stepleton/voltmitten/powerup/mos_dram-1979_Mostek_Memory_Data_Book_and_Designers_Guide_Mar79-p108.png

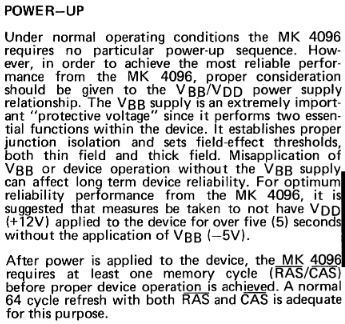
powerup/mos_dram-1979_Mostek_Memory_Data_Book_and_Designers_Guide_Mar79-p108.png
