stepleton/voltmitten/hardware/voltmitten.sch

## KiCad design hardware/voltmitten.sch (2021-11-13)

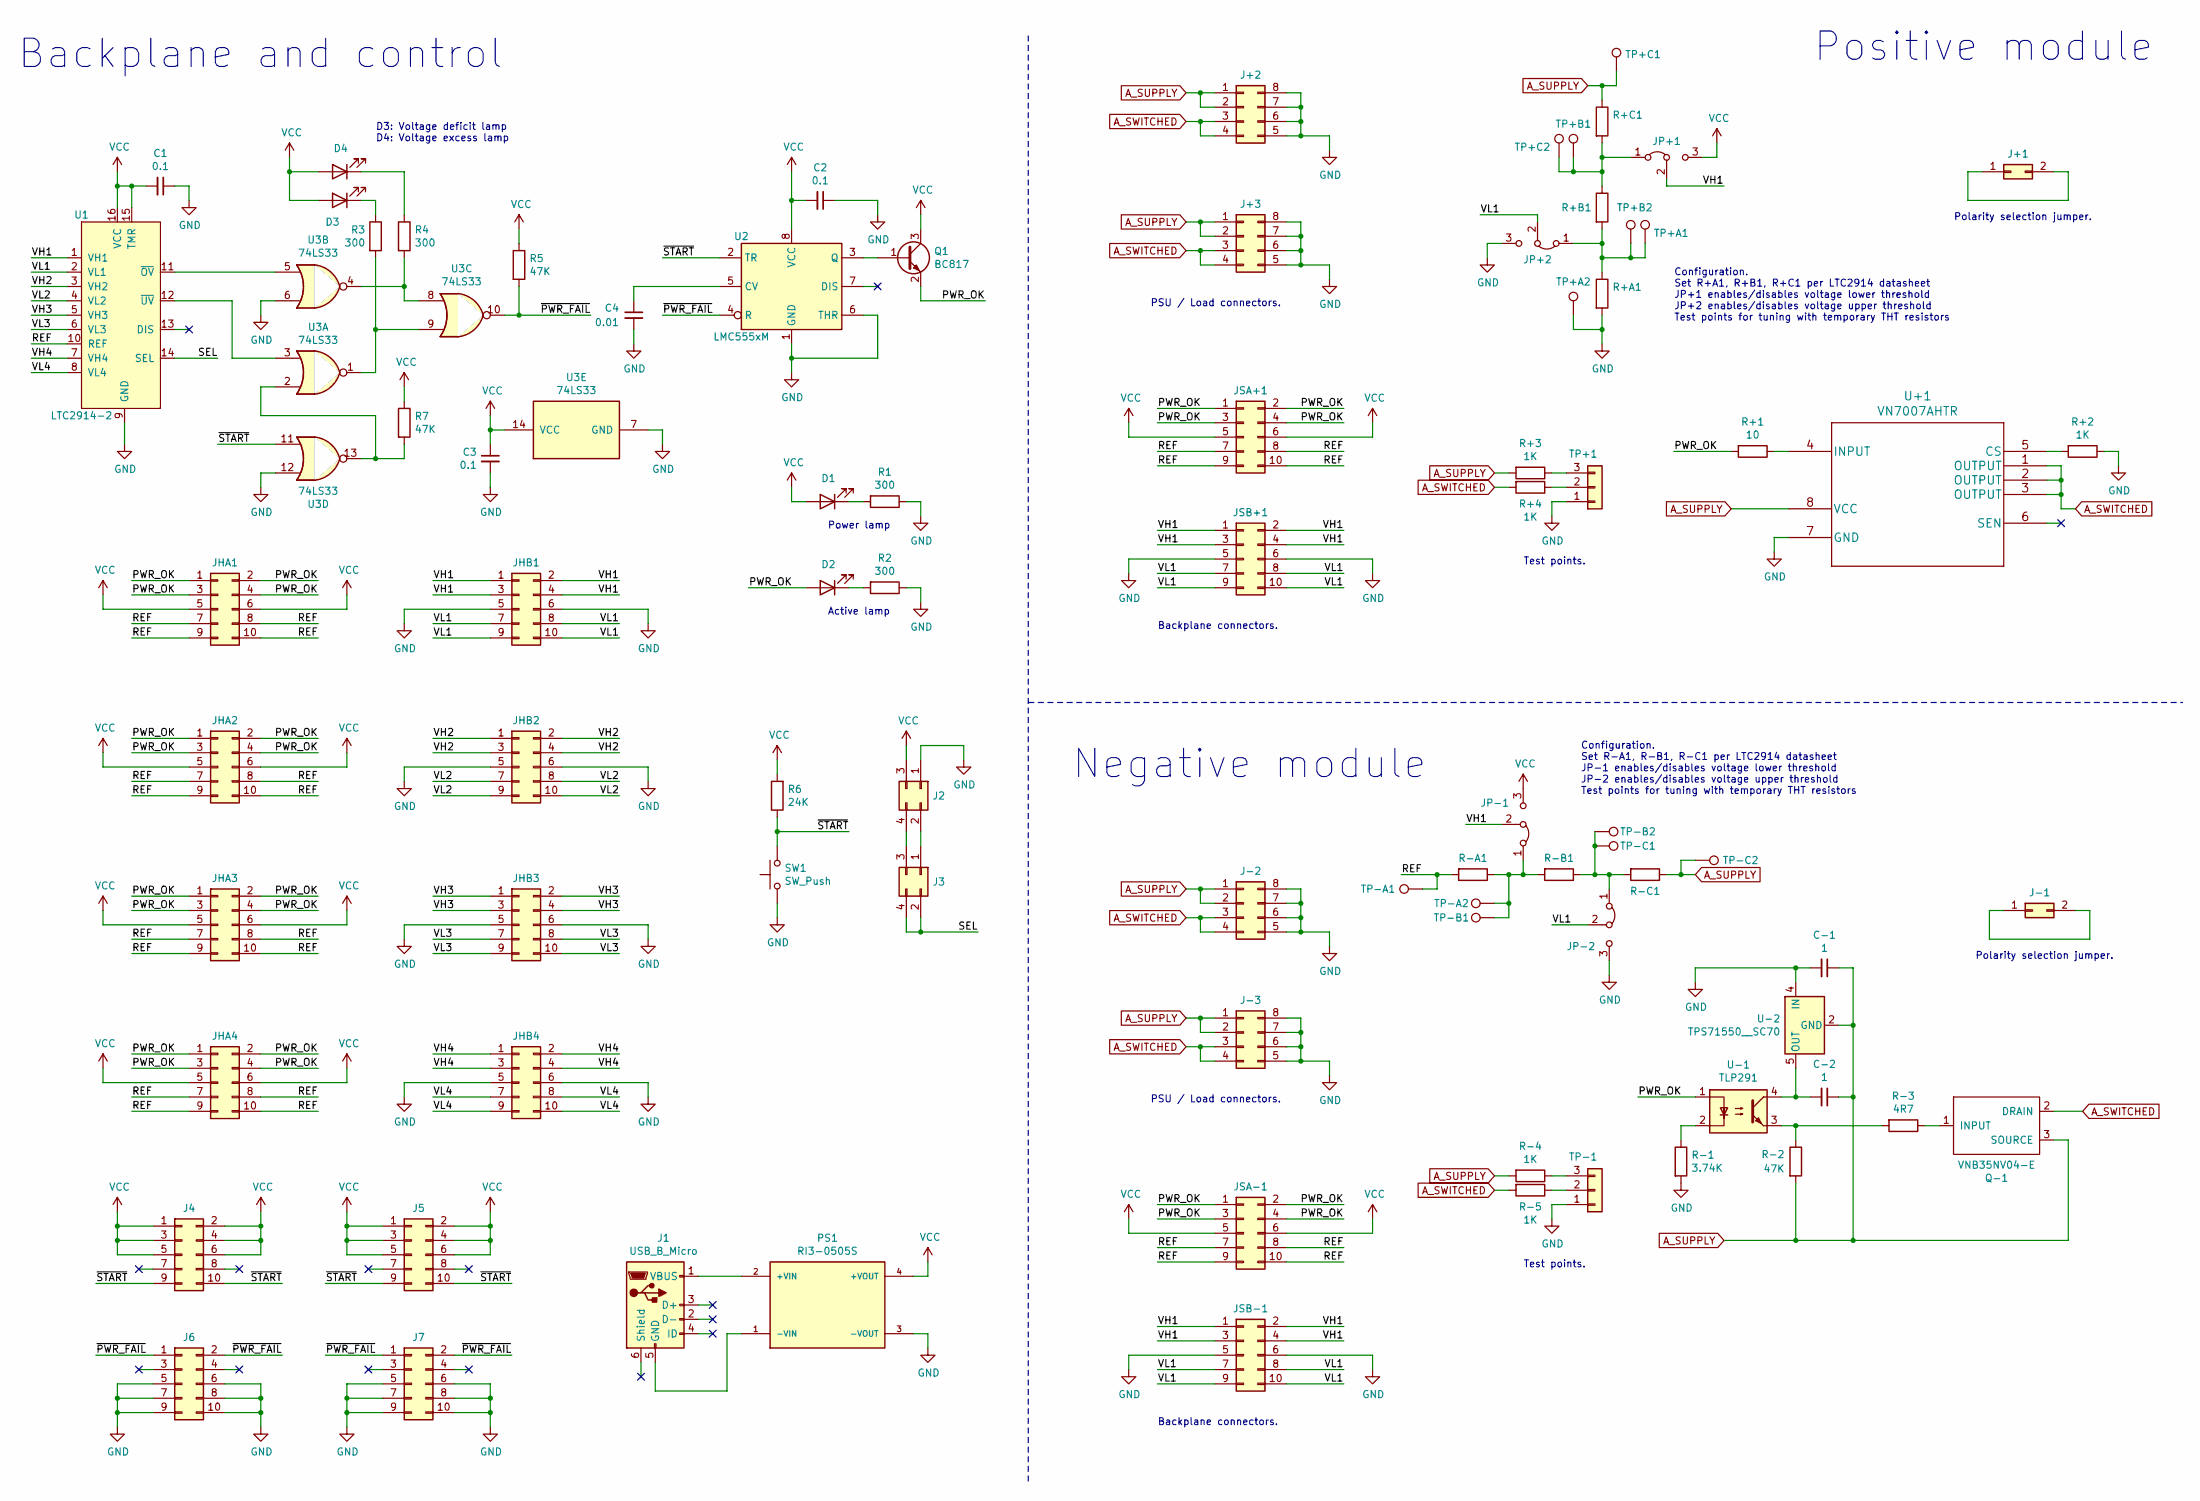
[picture p31: schematic voltmitten.sch]

Parts:
C1, C2, C3: 0.1; C_0603_1608Metric_Pad1.08x0.95mm_HandSolder
C4: 0.01; C_0603_1608Metric_Pad1.08x0.95mm_HandSolder
C-1, C-2: 1; C_0603_1608Metric_Pad1.08x0.95mm_HandSolder
D1, D2, D3, D4: SML-D12U1WT86‎; LED_0603_1608Metric_Pad1.05x0.95mm_HandSolder
J1: USB_B_Micro; USB_Micro-B_Amphenol_10103594-0001LF_Horizontal
J2, J3: Conn_02x02_Row_Letter_Last; PinSocket_2x02_P2.54mm_Vertical
J4, J6: Conn_02x05_Row_Letter_Last; PinHeader_2x05_P2.54mm_Horizontal
J5, J7: Conn_02x05_Row_Letter_Last; PinSocket_2x05_P2.54mm_Horizontal
J+1: Conn_02x01; PinHeader_1x02_P2.54mm_Vertical
J+2, J+3: Conn_02x04_Counter_Clockwise; TE_MATE-N-LOK_1-794073-x_2x04_P4.14mm_Vertical_no_boardlock
J-1: Conn_02x01; PinHeader_1x02_P2.54mm_Vertical
J-2, J-3: Conn_02x04_Counter_Clockwise; TE_MATE-N-LOK_1-794073-x_2x04_P4.14mm_Vertical_no_boardlock
JHA1, JHA2, JHA3, JHA4: Conn_02x05_Row_Letter_Last; PinHeader_2x05_P2.54mm_Vertical
JHB1, JHB2, JHB3, JHB4: Conn_02x05_Row_Letter_Last; PinHeader_2x05_P2.54mm_Vertical
JP+1, JP+2: Jumper_3_Bridged12; PinHeader_1x03_P2.00mm_Horizontal
JP-1, JP-2: Jumper_3_Bridged12; PinHeader_1x03_P2.00mm_Horizontal
JSA+1: Conn_02x05_Odd_Even; PinSocket_2x05_P2.54mm_Vertical
JSA-1: Conn_02x05_Odd_Even; PinSocket_2x05_P2.54mm_Vertical
JSB+1: Conn_02x05_Odd_Even; PinSocket_2x05_P2.54mm_Vertical
JSB-1: Conn_02x05_Odd_Even; PinSocket_2x05_P2.54mm_Vertical
PS1: RI3-0505S; CONV_RI3-0505S; PARTREV 3
Q1: BC817; SOT-23
Q-1: VNB35NV04-E; D2PAK
R1, R2, R3, R4: 300; R_0603_1608Metric_Pad0.98x0.95mm_HandSolder
R5, R7: 47K; R_0603_1608Metric_Pad0.98x0.95mm_HandSolder
R6: 24K; R_0603_1608Metric_Pad0.98x0.95mm_HandSolder
R+1: 10; R_0603_1608Metric_Pad0.98x0.95mm_HandSolder
R+2, R+3, R+4: 1K; R_0603_1608Metric_Pad0.98x0.95mm_HandSolder
R+A1: R; R_0603_1608Metric_Pad0.98x0.95mm_HandSolder
R+B1: R; R_0603_1608Metric_Pad0.98x0.95mm_HandSolder
R+C1: R; R_0603_1608Metric_Pad0.98x0.95mm_HandSolder
R-1: 3.74K; R_0603_1608Metric_Pad0.98x0.95mm_HandSolder
R-2: 47K; R_0603_1608Metric_Pad0.98x0.95mm_HandSolder
R-3: 4R7; R_0603_1608Metric_Pad0.98x0.95mm_HandSolder
R-4, R-5: 1K; R_0603_1608Metric_Pad0.98x0.95mm_HandSolder
R-A1: R; R_0603_1608Metric_Pad0.98x0.95mm_HandSolder
R-B1: R; R_0603_1608Metric_Pad0.98x0.95mm_HandSolder
R-C1: R; R_0603_1608Metric_Pad0.98x0.95mm_HandSolder
SW1: SW_Push; SW_PUSH_6mm
TP+1: Conn_01x03; PinHeader_1x03_P2.54mm_Vertical
TP+A1, TP+A2: TestPoint; TestPointTiny
TP+B1, TP+B2: TestPoint; TestPointTiny
TP+C1, TP+C2: TestPoint; TestPointTiny
TP-1: Conn_01x03; PinHeader_1x03_P2.54mm_Vertical
TP-A1, TP-A2: TestPoint; TestPointTiny
TP-B1, TP-B2: TestPoint; TestPointTiny
TP-C1, TP-C2: TestPoint; TestPointTiny
U1: LTC2914-2; SSOP-16_3.9x4.9mm_P0.635mm
U2: LMC555xM; SOIC-8_3.9x4.9mm_P1.27mm
U3: 74LS33; SOIC-14_3.9x8.7mm_P1.27mm
U+1: VN7007AHTR; OCTOPAK_STM
U-1: TLP291; SOIC-4_4.55x2.6mm_P1.27mm
U-2: TPS71550__SC70; SOT-353_SC-70-5

Connections:
A_SUPPLY: C-1.1, C-2.1, J+2.1, J+2.2, J+3.1, J+3.2, J-2.1, J-2.2, J-3.1, J-3.2, Q-1.3 (SOURCE), R+3.2, R+C1.1, R-2.2, R-4.2, R-C1.1, TP+C1.1, TP-C2.1, U+1.8 (VCC), U-2.2 (GND)
A_SWITCHED: J+2.3, J+2.4, J+3.3, J+3.4, J-2.3, J-2.4, J-3.3, J-3.4, Q-1.2 (DRAIN), R+4.2, R-5.2, U+1.1 (OUTPUT), U+1.2 (OUTPUT), U+1.3 (OUTPUT)
GND: C1.1, C2.1, C3.2, C4.2, C-1.2, J2.1, J6.5, J6.6, J6.7, J6.8, J6.9, J6.10, J7.5, J7.6, J7.7, J7.8, J7.9, J7.10, J+2.5, J+2.6, J+2.7, J+2.8, J+3.5, J+3.6, J+3.7, J+3.8, J-2.5, J-2.6, J-2.7, J-2.8, J-3.5, J-3.6, J-3.7, J-3.8, JHB1.5, JHB1.6, JHB2.5, JHB2.6, JHB3.5, JHB3.6, JHB4.5, JHB4.6, JP+2.3 (B), JP-2.3 (B), JSB+1.5, JSB+1.6, JSB-1.5, JSB-1.6, PS1.3 (-VOUT), R1.1, R2.1, R+2.1, R+A1.2, R-1.2, SW1.1, TP+1.1, TP+A2.1, TP-1.1, U1.9 (GND), U2.1 (GND), U2.6 (THR), U3.6, U3.7 (GND), U3.12, U+1.7 (GND), U-2.4 (IN)
unnamed: C4.1, U2.5 (CV)
unnamed: C-2.2, U-1.4, U-2.5 (OUT)
unnamed: D1.1 (K), R1.2
unnamed: D2.1 (K), R2.2
unnamed: D3.1 (K), R3.1
unnamed: D4.1 (K), R4.1
unnamed: J1.1 (VBUS), PS1.2 (+VIN)
unnamed: J1.5 (GND), PS1.1 (-VIN)
unnamed: J2.2, J3.1
unnamed: J2.4, J3.3
unnamed: J+1.1, J+1.2
unnamed: J-1.1, J-1.2
unnamed: JP+1.1 (A), R+B1.1, R+C1.2, TP+B1.1, TP+C2.1
unnamed: JP+2.1 (A), R+A1.1, R+B1.2, TP+A1.1, TP+B2.1
unnamed: JP-1.1 (A), R-A1.1, R-B1.2, TP-A2.1, TP-B1.1
unnamed: JP-2.1 (A), R-B1.1, R-C1.2, TP-B2.1, TP-C1.1
unnamed: Q1.1 (B), U2.3 (Q)
unnamed: Q-1.1 (INPUT), R-3.1
unnamed: R3.2, U3.1, U3.9
unnamed: R4.2, U3.4, U3.8
unnamed: R7.2, U3.2, U3.13
unnamed: R+1.1, U+1.4 (INPUT)
unnamed: R+2.2, U+1.5 (CS)
unnamed: R+3.1, TP+1.3
unnamed: R+4.1, TP+1.2
unnamed: R-1.1, U-1.2
unnamed: R-2.1, R-3.2, U-1.3
unnamed: R-4.1, TP-1.3
unnamed: R-5.1, TP-1.2
unnamed: U1.11 (~OV), U3.5
unnamed: U1.12 (~UV), U3.3
PWR_OK: D2.2 (A), JHA1.1, JHA1.2, JHA1.3, JHA1.4, JHA2.1, JHA2.2, JHA2.3, JHA2.4, JHA3.1, JHA3.2, JHA3.3, JHA3.4, JHA4.1, JHA4.2, JHA4.3, JHA4.4, JSA+1.1, JSA+1.2, JSA+1.3, JSA+1.4, JSA-1.1, JSA-1.2, JSA-1.3, JSA-1.4, Q1.2 (E), R+1.2, U-1.1
REF: JHA1.7, JHA1.8, JHA1.9, JHA1.10, JHA2.7, JHA2.8, JHA2.9, JHA2.10, JHA3.7, JHA3.8, JHA3.9, JHA3.10, JHA4.7, JHA4.8, JHA4.9, JHA4.10, JSA+1.7, JSA+1.8, JSA+1.9, JSA+1.10, JSA-1.7, JSA-1.8, JSA-1.9, JSA-1.10, R-A1.2, TP-A1.1, U1.10 (REF)
SEL: J3.2, J3.4, U1.14 (SEL)
VCC: C1.2, C2.2, C3.1, D1.2 (A), D3.2 (A), D4.2 (A), J2.3, J4.1, J4.2, J4.3, J4.4, J4.5, J4.6, J5.1, J5.2, J5.3, J5.4, J5.5, J5.6, JHA1.5, JHA1.6, JHA2.5, JHA2.6, JHA3.5, JHA3.6, JHA4.5, JHA4.6, JP+1.3 (B), JP-1.3 (B), JSA+1.5, JSA+1.6, JSA-1.5, JSA-1.6, PS1.4 (+VOUT), Q1.3 (C), R5.1, R6.2, R7.1, U1.15 (TMR), U1.16 (VCC), U2.8 (VCC), U3.14 (VCC)
VH1: JHB1.1, JHB1.2, JHB1.3, JHB1.4, JP+1.2 (C), JP-1.2 (C), JSB+1.1, JSB+1.2, JSB+1.3, JSB+1.4, JSB-1.1, JSB-1.2, JSB-1.3, JSB-1.4, U1.1 (VH1)
VH2: JHB2.1, JHB2.2, JHB2.3, JHB2.4, U1.3 (VH2)
VH3: JHB3.1, JHB3.2, JHB3.3, JHB3.4, U1.5 (VH3)
VH4: JHB4.1, JHB4.2, JHB4.3, JHB4.4, U1.7 (VH4)
VL1: JHB1.7, JHB1.8, JHB1.9, JHB1.10, JP+2.2 (C), JP-2.2 (C), JSB+1.7, JSB+1.8, JSB+1.9, JSB+1.10, JSB-1.7, JSB-1.8, JSB-1.9, JSB-1.10, U1.2 (VL1)
VL2: JHB2.7, JHB2.8, JHB2.9, JHB2.10, U1.4 (VL2)
VL3: JHB3.7, JHB3.8, JHB3.9, JHB3.10, U1.6 (VL3)
VL4: JHB4.7, JHB4.8, JHB4.9, JHB4.10, U1.8 (VL4)
~PWR_FAIL: J6.1, J6.2, J7.1, J7.2, R5.2, U2.4 (R), U3.10
~START: J4.9, J4.10, J5.9, J5.10, R6.1, SW1.2, U2.2 (TR), U3.11

Notes on the sheet:
Backplane and control
Negative module
Configuration. Set R+A1, R+B1, R+C1 per LTC2914 datasheet JP+1 enables/disables voltage lower threshold JP+2 enables/disables voltage upper threshold Test points for tuning with temporary THT resistors
Backplane connectors.
PSU / Load connectors.
Polarity selection jumper.
Configuration. Set R-A1, R-B1, R-C1 per LTC2914 datasheet JP-1 enables/disables voltage lower threshold JP-2 enables/disables voltage upper threshold Test points for tuning with temporary THT resistors
Positive module
Test points.
Power lamp
Active lamp
D3: Voltage deficit lamp D4: Voltage excess lamp
